jorge-pais/PE_universal12Vsupply/simulationModels/sim.asc

C1: cap; 560p
C2: cap; 33n
C3: cap; 68µ
C4: cap; 10µ
C5: cap; 15µ
C6: cap; 15µ
C7: cap; 15µ
C8: cap; 100n
C9: cap; 220p
C10: cap; 100n
C11: cap; 100n
C12: cap; 1µ
C13: cap; 100n
C14: cap; 100n
C15: cap; 47p
C16: cap; 15µ
C17: cap; 15µ
C18: cap; 15µ
C19: cap; 470µ
D1: diode; Dss24
D2: diode; Dss24
D3: diode; Dss24
D4: diode; Dss24
D5: diode; Dss24
L1: ind; 4.7µ
M1: nmos; BSC031N06NS3
M2: nmos; BSC031N06NS3
M3: nmos; BSC031N06NS3
M4: nmos; BSC031N06NS3
R1: res; 10k
R2: res; 105k
R3: res; 7.5k
R4: res; 10
R5: res; 249k
R6: res; 59k
R7: res; 93.1k
R8: res; 27.4k
R9: res; 10k
R10: res; 8m
R11: res; 100
R12: res; 100
R13: res; 2k
U1: LM5175_TRANS
V1: voltage; 5
Named nets: 0, COMP, Vout, FB, Vin, ICVin, EN, CSG, Vcc, LDRV2, HDRV2, LDRV1, HDRV1, BOOT1, BOOT2, SW1, SW2, CS
.lib /home/jorgep/OneDrive/Faculdade/Mestrado/2Ano/PowerElectronics/project/simulationModels/LM5175_TRANS.lib
.lib /home/jorgep/OneDrive/Faculdade/Mestrado/2Ano/PowerElectronics/project/simulationModels/SS24T3.REV0.lib
.tran 2
